AI6YP/vernier/sw/main/iosevka.h

/*
................ .......@@@@@@@@@ @@@@@@@@@....... ................ ................ ..............@@ @@@@@@@@@....... ................ ................ ......@@@@@@@@@@ @@@@@@@@@....... ................ ................ .......@@@@@@@@@ @@@@@@@@@@...... ................ ................ ................ ......@@@@@@@@@@ @............... .........@@@@@@@ @@@@@@@@@@@@@@@@ @@@@@@@@@@@@@@@@ @@@@@........... ................ ................ @@@@@@@@@@...... ................ ........@@@@@@@@ @@@@@@@@@@@@@@@@ @@@@@@@@@@@@@@@@ @@@@@@@@........ ................ .......@@@@@@@@@ @@@@@@@@@....... ................ ................ .......@@@@@@@@@ @@@@@@@@@....... ................ ................ ................ ................ ................
................ ....@@@@@@@@@@@@ @@@@@@@@@@@@.... ................ ................ .............@@@ @@@@@@@@@....... ................ ................ ....@@@@@@@@@@@@ @@@@@@@@@@@@.... ................ ................ ....@@@@@@@@@@@@ @@@@@@@@@@@@.... ................ ................ ................ ......@@@@@@@@@@ ................ .........@@@@@@@ @@@@@@@@@@@@@@@@ @@@@@@@@@@@@@@@@ @@@@@........... ................ ...............@ @@@@@@@@@@...... ................ ........@@@@@@@@ @@@@@@@@@@@@@@@@ @@@@@@@@@@@@@@@@ @@@@@@@@........ ................ ....@@@@@@@@@@@@ @@@@@@@@@@@@.... ................ ................ .....@@@@@@@@@@@ @@@@@@@@@@@..... ................ ................ ................ ................ ................
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
*/
#ifndef _IOSEVKA_64_96_H_
#define _IOSEVKA_64_96_H_

// Width: 704 Height: 96
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
